JuanaNasi/Fantomas_ECG/software/Fantomas_final/ECGBancos_PTBXL_recortado.h

// ECGBancos_PTBXL_recortado.h
// Archivo generado desde PTB-XL records100.
// Cada matriz contiene 1 latido recortado de 80 muestras x 8 canales.
// Frecuencia original: 100 Hz -> PeriodoDeMuestreo recomendado: 10 ms.
// Canales seleccionados: I, II, V1, V2, V3, V4, V5, V6.
// Recorte usado: 25 muestras antes del pico R y 55 muestras despues.
// Escalado: valor_pwm = 30000 + 4000 * senial_mV_centrada.
// Rango limitado a 0..60000 para setPWM_Int().

#ifndef ECGBANCOS_PTBXL_RECORTADO_H
#define ECGBANCOS_PTBXL_RECORTADO_H

#include <stdint.h>

#define CANTIDAD_CANALES_ECG 8
#define PERIODO_MUESTREO_PTBXL_MS 10
#define VALOR_LINEA_BASE_ECG 30000

// DatosNormal: Normal | Registro PTB-XL: 00003_lr | Clase: NORM | Pico R aprox muestra 857
#define N_DatosNormal 80
const uint16_t DatosNormal[N_DatosNormal][CANTIDAD_CANALES_ECG] = {
  {29976, 29936, 30088, 29778, 29844, 29844, 29916, 29868},
  {29924, 29928, 30068, 29782, 29844, 29860, 29916, 29864},
  {29956, 29956, 30056, 29774, 29844, 29844, 29908, 29852},
  {29936, 29968, 30040, 29758, 29844, 29832, 29892, 29836},
  {30068, 30080, 30012, 29758, 29824, 29840, 29900, 29832},
  {30060, 30144, 29972, 29762, 29828, 29816, 29904, 29828},
  {30000, 30152, 29944, 29790, 29800, 29820, 29924, 29836},
  {29992, 30236, 29896, 29722, 29740, 29808, 29928, 29828},
  {30048, 30424, 29828, 29682, 29776, 29764, 29944, 29836},
  {30164, 30588, 29864, 29746, 29796, 29828, 29956, 29832},
  {30172, 30604, 29976, 29798, 29868, 29984, 29960, 29836},
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
  {30036, 29924, 30112, 30148, 30506, 29754, 29506, 30698},
  {30084, 29964, 30096, 30116, 30550, 29858, 29558, 30686},
  {30096, 29960, 30080, 30124, 30606, 29910, 29578, 30722},
  {30124, 30036, 30048, 30116, 30646, 29994, 29598, 30802},
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
};

#endif
