JuanaNasi/Fantomas_ECG/software/Fantomas_anteriores/Fantomas_5bancos/ECGBancos_PTBXL.h

// ECGBancos_PTBXL.h
// Archivo generado desde registros PTB-XL records100.
// Cada matriz tiene 1000 muestras x 8 canales.
// Frecuencia original: 100 Hz -> PeriodoDeMuestreo recomendado: 10 ms.
// Canales seleccionados de las 12 derivaciones: I, II, V1, V2, V3, V4, V5, V6.
// Escalado usado: valor_pwm = 30000 + 4000 * señal_mV_centrada.
// Rango de salida limitado a 0..60000 para setPWM_Int().

#ifndef ECGBANCOS_PTBXL_H
#define ECGBANCOS_PTBXL_H

#include <stdint.h>

#define CANTIDAD_CANALES_ECG 8
#define PERIODO_MUESTREO_PTBXL_MS 10

// DatosNormal: Normal | Registro PTB-XL: 00003_lr | Código: NORM
#define N_DatosNormal 1000
const uint16_t DatosNormal[N_DatosNormal][CANTIDAD_CANALES_ECG] = {
  {30032, 29696, 29948, 29714, 29640, 29684, 29752, 29788},
  {30008, 29732, 29980, 29730, 29624, 29680, 29740, 29780},
  {29932, 29784, 30004, 29726, 29684, 29784, 29792, 29836},
  {29836, 29532, 30048, 29898, 29732, 29704, 29704, 29768},
  {29796, 29768, 30164, 30246, 30072, 29984, 29972, 29980},
  {30060, 29944, 30256, 30474, 30924, 30720, 30444, 30304},
  {31532, 31016, 29896, 31050, 32384, 32152, 31612, 31308},
  {33284, 32300, 28112, 29110, 33376, 33700, 32840, 32412},
  {31852, 31004, 26952, 25794, 29200, 30740, 30784, 31008},
  {29844, 29872, 28376, 27242, 27096, 28664, 29356, 29804},
  {29976, 29644, 29796, 29854, 29432, 29624, 29784, 29884},
  {29948, 29524, 29956, 29950, 29608, 29680, 29660, 29908},
  {29880, 29652, 30020, 29982, 29696, 29892, 29792, 29964},
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
  {30304, 30284, 29976, 30020, 30538, 30646, 30990, 30562},
  {30200, 30092, 30004, 29928, 30286, 30334, 30658, 30366},
  {30172, 29976, 30024, 29852, 30086, 30110, 30386, 30218},
  {30192, 29912, 30020, 29812, 29906, 29938, 30234, 30110},
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
};

#endif
